hwkim3330/elite-t1s-hat/firmware/t1s_node/src/lan865x/esp_eth_mac_lan865x.h

/*
 * SPDX-FileCopyrightText: 2025 Espressif Systems (Shanghai) CO LTD
 *
 * SPDX-License-Identifier: Apache-2.0
 */

#pragma once

#include "esp_eth_mac.h"
#include "esp_idf_version.h"
#if ESP_IDF_VERSION >= ESP_IDF_VERSION_VAL(5, 3, 0)
#include "esp_eth_mac_spi.h"
#endif
#include "driver/spi_master.h"

#ifdef __cplusplus
extern "C" {
#endif
/**
 * @brief LAN865x specific configuration
 *
 */
typedef struct {
    spi_host_device_t spi_host_id;                      /*!< SPI host id */
    spi_device_interface_config_t *spi_devcfg;          /*!< SPI device configuration */
    int int_gpio_num;                                   /*!< Interrupt GPIO number, set to -1 if no interrupt */
    uint32_t poll_period_ms;                            /*!< Polling period in milliseconds if no interrupt */
    eth_spi_custom_driver_config_t custom_spi_driver;   /*!< Custom SPI driver configuration, optional */
} eth_lan865x_config_t;

/**
 * @brief Default LAN865x specific configuration
 *
 */
#define ETH_LAN865X_DEFAULT_CONFIG(spi_host, spi_devcfg_p) \
    {                                           \
        .int_gpio_num = 4,                      \
        .poll_period_ms = 0,                    \
        .spi_host_id = spi_host,                \
        .spi_devcfg = spi_devcfg_p,             \
        .custom_spi_driver = ETH_DEFAULT_SPI,   \
    }

/**
 * @brief Create a new LAN865x Ethernet MAC driver
 *
 * @param lan865x_config: LAN865x specific configuration
 * @param mac_config: Ethernet MAC configuration
 *
 * @return
 *      - esp_eth_mac_t: handle of Ethernet MAC driver
 *      - NULL: failed to create MAC driver
 */
esp_eth_mac_t *esp_eth_mac_new_lan865x(const eth_lan865x_config_t *lan865x_config, const eth_mac_config_t *mac_config);

/* LOCAL PATCH (t1s_hat): raw register access, under the driver's SPI lock. mms is the
 * OPEN Alliance memory map selector (0 OA, 1 MAC, 2 PCS, 3 PMA, 4 PHY vendor, 10 misc). */
esp_err_t esp_eth_mac_lan865x_read_reg(esp_eth_mac_t *mac, uint8_t mms, uint16_t addr, uint32_t *value);
esp_err_t esp_eth_mac_lan865x_write_reg(esp_eth_mac_t *mac, uint8_t mms, uint16_t addr, uint32_t value);

/* LOCAL PATCH (t1s_hat): frame timestamping. rx: called from the driver's RX task for every frame
 * that arrived with a prepended timestamp (OA_CONFIG0.FTSE/FTSS set), ts = seconds << 32 | ns of the
 * chip's wall clock; frame is the frame without it. tx: called per transmitted frame; return true to
 * have its egress time captured into TTSCAH/L (STATUS0.TTSCAA). Both run in driver context: keep short. */
typedef void (*esp_eth_mac_lan865x_rx_ts_cb_t)(const uint8_t *frame, uint32_t len, uint64_t ts);
typedef bool (*esp_eth_mac_lan865x_tx_ts_cb_t)(const uint8_t *frame, uint32_t len);
void esp_eth_mac_lan865x_set_ts_hooks(esp_eth_mac_lan865x_rx_ts_cb_t rx, esp_eth_mac_lan865x_tx_ts_cb_t tx);

#ifdef __cplusplus
}
#endif
